sebastienroy/shutter_speed_tester/Development/04_Casing/parts/white/CasingForShutterSpeedTester-Door.stl

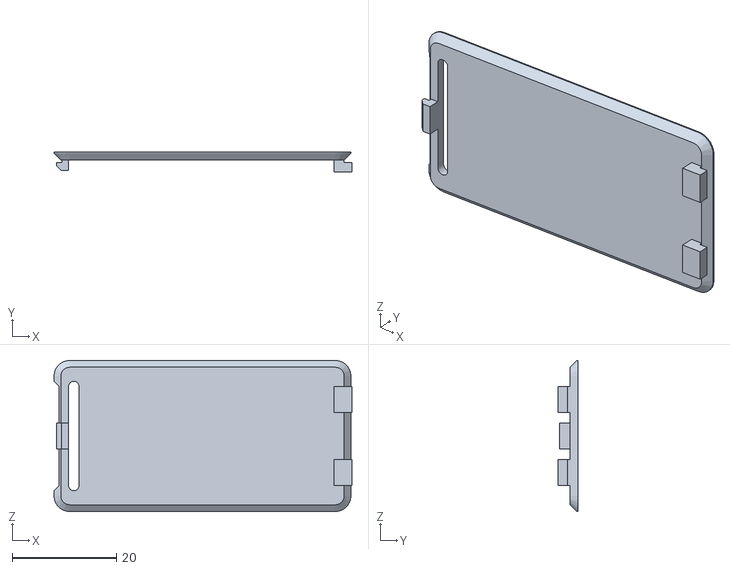
[picture p44: CAD file, 2022-01-18]
Development/04_Casing/parts/white/CasingForShutterSpeedTester-Door.stl
57.2 x 3.80 x 29.0
