sebastienroy/shutter_speed_tester/Development/04_Casing/parts/white/CasingForShutterSpeedTester-CoverWireBlocker.stl

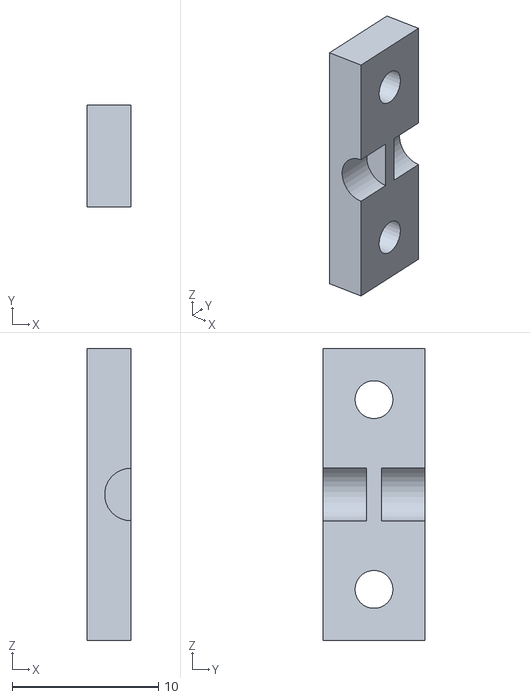
[picture p45: CAD file, 2022-01-18]
Development/04_Casing/parts/white/CasingForShutterSpeedTester-CoverWireBlocker.stl
3.00 x 7.00 x 20.0
