sebastienroy/shutter_speed_tester/Development/04_Casing/parts/white/LightSensorCasing-6x6Adapter.stl

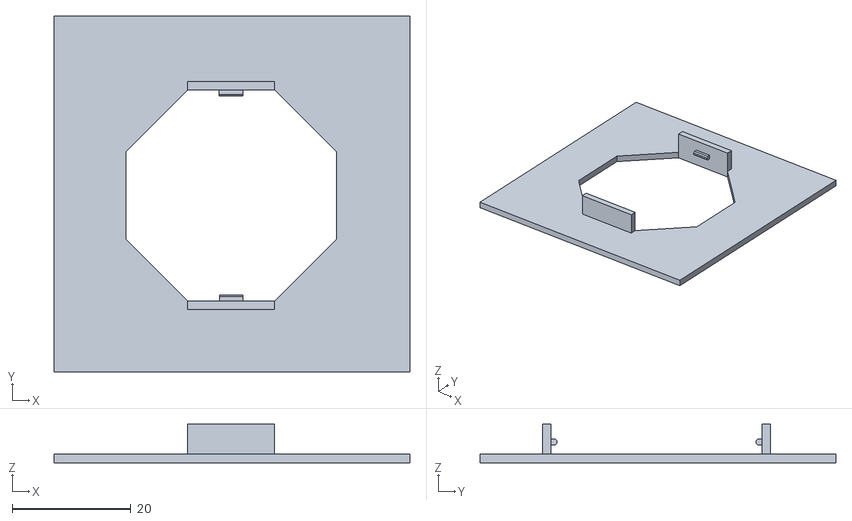
[picture p46: CAD file, 2022-01-18]
Development/04_Casing/parts/white/LightSensorCasing-6x6Adapter.stl
60.0 x 60.0 x 6.50
