sebastienroy/shutter_speed_tester/Development/04_Casing/parts/white/CasingForShutterSpeedTester-Calle_LED.stl

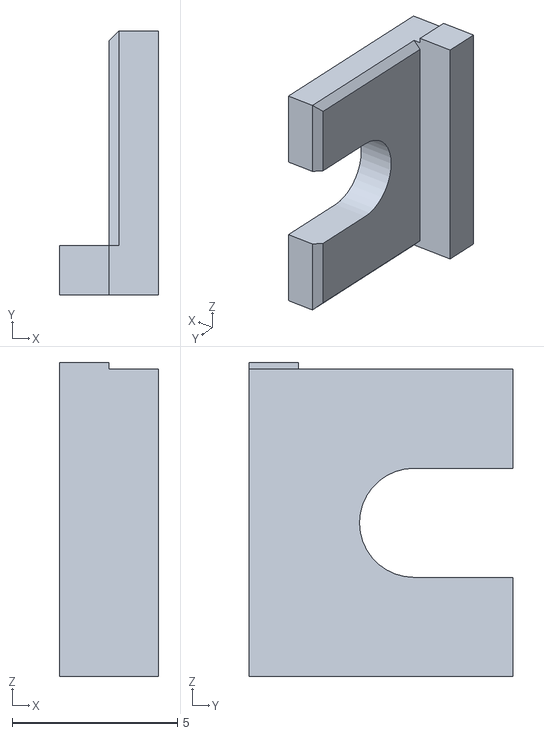
[picture p47: CAD file, 2022-01-18]
Development/04_Casing/parts/white/CasingForShutterSpeedTester-Calle_LED.stl
3.00 x 8.00 x 9.50
